BryanOrabutt/cse521_project/automated_functions/data/cattie1.png

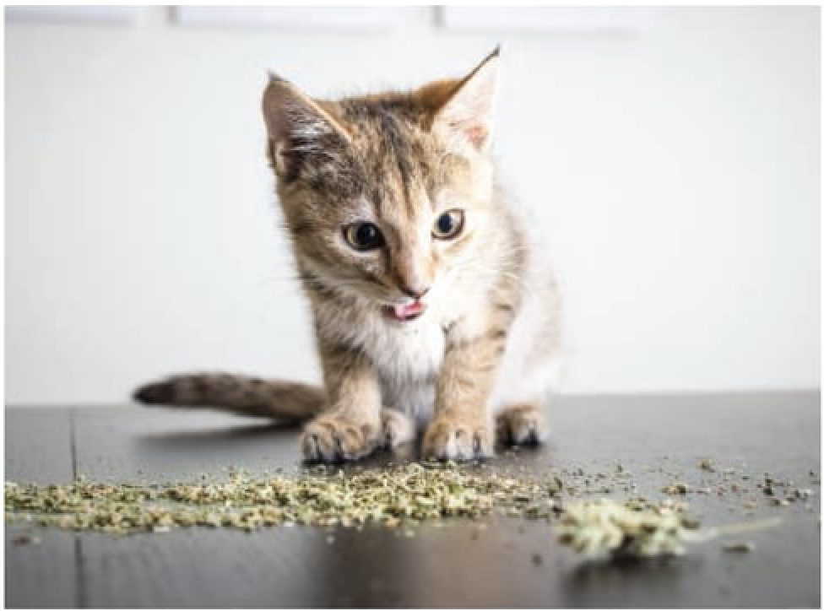
automated_functions/data/cattie1.png
