BryanOrabutt/cse521_project/automated_functions/data/69528761_480x640.jpg

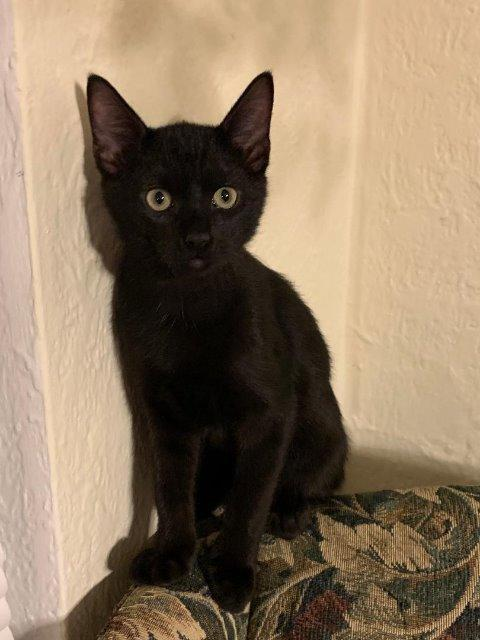
automated_functions/data/69528761_480x640.jpg
