BryanOrabutt/cse521_project/automated_functions/data/69528762_500x375.jpg

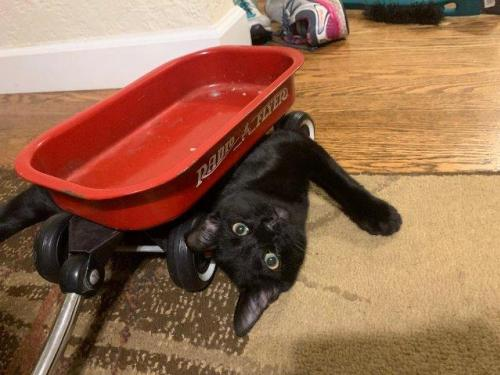
automated_functions/data/69528762_500x375.jpg
