BryanOrabutt/cse521_project/automated_functions/data/cat1.png

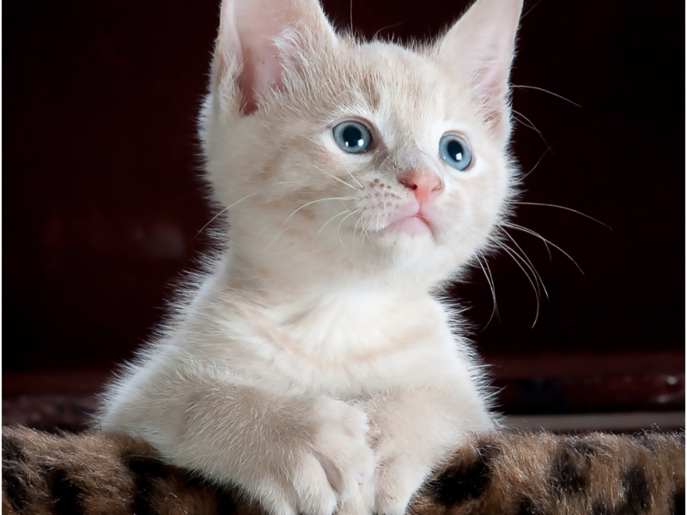
automated_functions/data/cat1.png
