BryanOrabutt/cse521_project/automated_functions/data/cat3.jpg

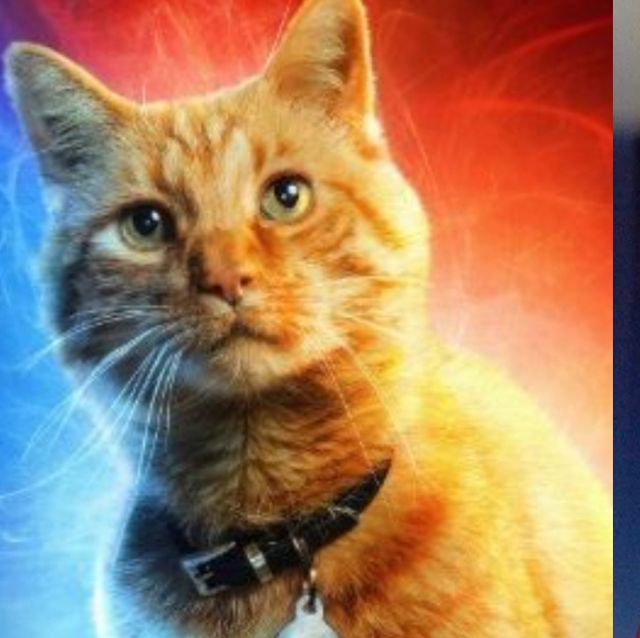
automated_functions/data/cat3.jpg
