BryanOrabutt/cse521_project/automated_functions/data/cat4.jpg

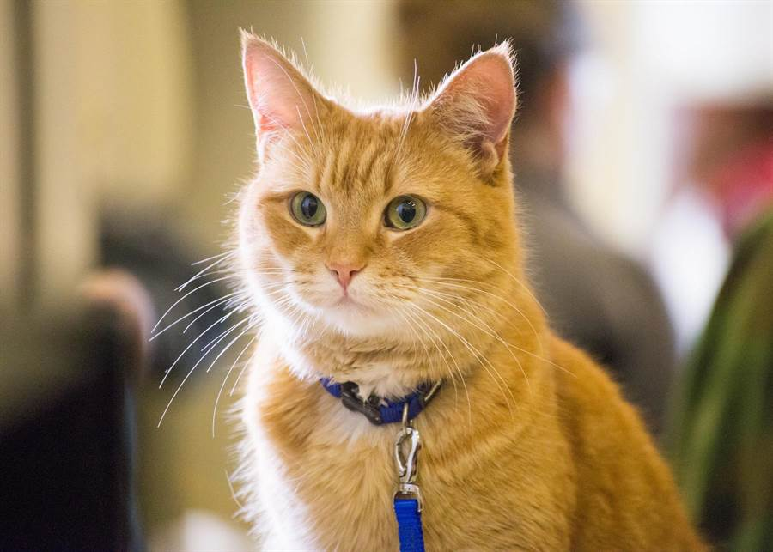
automated_functions/data/cat4.jpg
