BryanOrabutt/cse521_project/automated_functions/data/cat5.jpg

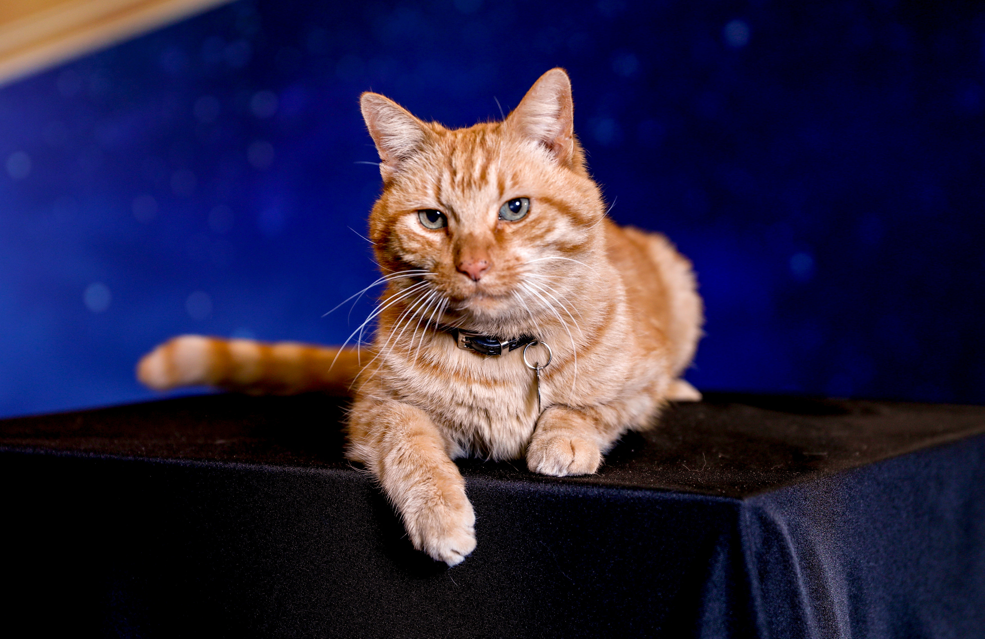
automated_functions/data/cat5.jpg
