BryanOrabutt/cse521_project/automated_functions/data/cattie2.png

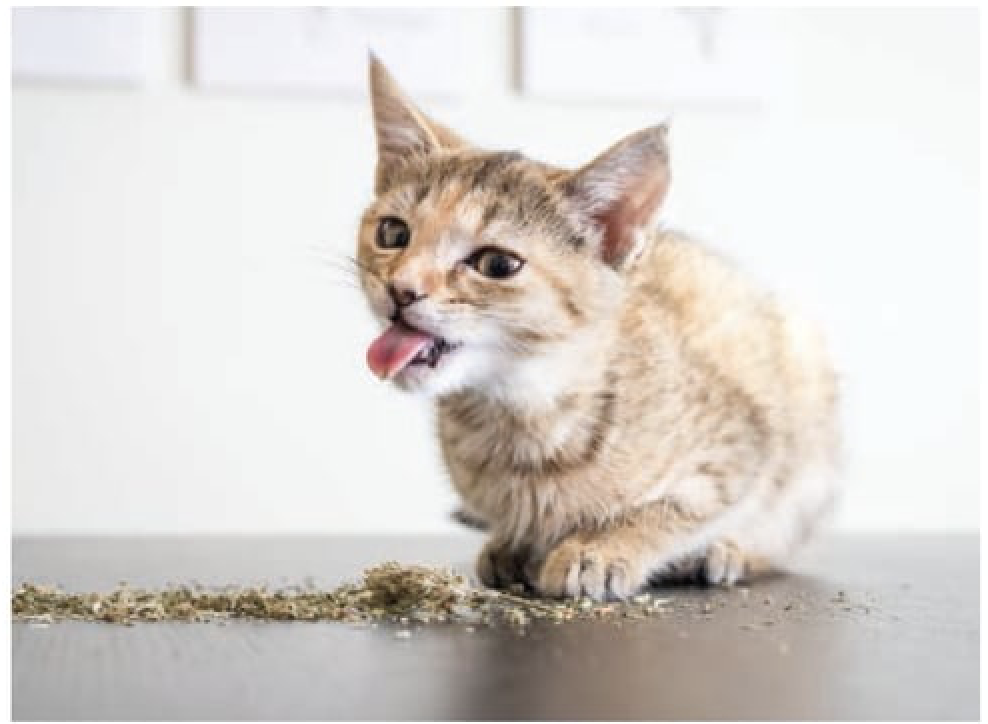
automated_functions/data/cattie2.png
