BryanOrabutt/cse521_project/automated_functions/data/cattie3.png

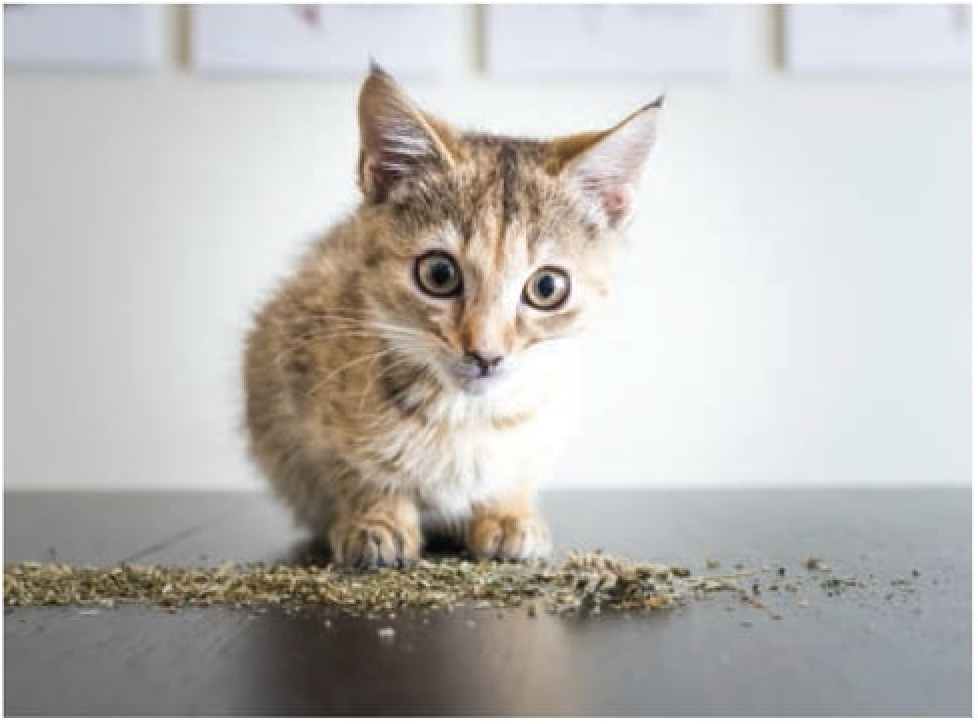
automated_functions/data/cattie3.png
