BryanOrabutt/cse521_project/automated_functions/data/cattie4.png

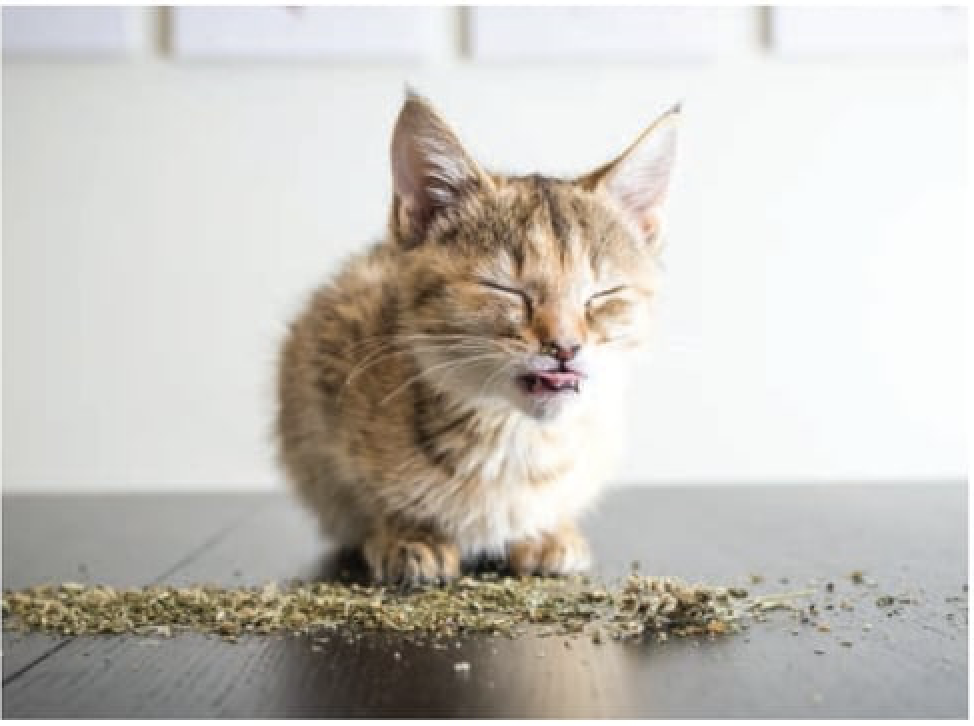
automated_functions/data/cattie4.png
