BryanOrabutt/cse521_project/espressif_code/examples/mcpwm_servo_control/main/mcpwm_servo_control_example.c

/* servo motor control example

   This example code is in the Public Domain (or CC0 licensed, at your option.)

   Unless required by applicable law or agreed to in writing, this
   software is distributed on an "AS IS" BASIS, WITHOUT WARRANTIES OR
   CONDITIONS OF ANY KIND, either express or implied.
*/
#include <stdio.h>

#include "freertos/FreeRTOS.h"
#include "freertos/task.h"
#include "freertos/timers.h"
#include "esp_attr.h"

#include "driver/mcpwm.h"
#include "soc/mcpwm_reg.h"
#include "soc/mcpwm_struct.h"

//You can get these value from the datasheet of servo you use, in general pulse width varies between 1000 to 2000 mocrosecond
#define SERVO_MIN_PULSEWIDTH 1000 //Minimum pulse width in microsecond
#define SERVO_MAX_PULSEWIDTH 2000 //Maximum pulse width in microsecond
#define SERVO_MAX_DEGREE 180 //Maximum angle in degree upto which servo can rotate

char flag = 0;

static void mcpwm_example_gpio_initialize()
{
    printf("initializing mcpwm servo control gpio......\n");
    mcpwm_gpio_init(MCPWM_UNIT_0, MCPWM0A, 18);    //Set GPIO 18 as PWM0A, to which servo is connected
}

/**
 * @brief Use this function to calcute pulse width for per degree rotation
 *
 * @param  degree_of_rotation the angle in degree to which servo has to rotate
 *
 * @return
 *     - calculated pulse width
 */
static uint32_t servo_per_degree_init(uint32_t degree_of_rotation)
{
    uint32_t cal_pulsewidth = 0;
    cal_pulsewidth = (SERVO_MIN_PULSEWIDTH + (((SERVO_MAX_PULSEWIDTH - SERVO_MIN_PULSEWIDTH) * (degree_of_rotation)) / (SERVO_MAX_DEGREE)));
    return cal_pulsewidth;
}

void servo_set(TimerHandle_t xTimer)
{
	uint32_t angle;
	if(flag)
	{
		flag = 0;
		angle = servo_per_degree_init(SERVO_MAX_DEGREE);
		printf("Angle set to: %d\n", SERVO_MAX_DEGREE);
	}
	else
	{
		flag = 1;
		angle = servo_per_degree_init(0);
		printf("Angle set to: %d\n", 0);
	}

	printf("Pulse width set to: %d us\n", angle);

	mcpwm_set_duty_in_us(MCPWM_UNIT_0, MCPWM_TIMER_0, MCPWM_OPR_A, angle);
}

void app_main()
{
    printf("Testing servo motor.......\n");
    //xTaskCreate(mcpwm_example_servo_control, "mcpwm_example_servo_control", 4096, NULL, 5, NULL);'

    //1. mcpwm gpio initialization
    mcpwm_example_gpio_initialize();

    //2. initial mcpwm configuration
    printf("Configuring Initial Parameters of mcpwm......\n");
    mcpwm_config_t pwm_config;
    pwm_config.frequency = 50;    //frequency = 50Hz, i.e. for every servo motor time period should be 20ms
    pwm_config.cmpr_a = 0;    //duty cycle of PWMxA = 0
    pwm_config.cmpr_b = 0;    //duty cycle of PWMxb = 0
    pwm_config.counter_mode = MCPWM_UP_COUNTER;
    pwm_config.duty_mode = MCPWM_DUTY_MODE_0;
    mcpwm_init(MCPWM_UNIT_0, MCPWM_TIMER_0, &pwm_config);    //Configure PWM0A & PWM0B with above settings
	
	TimerHandle_t t0 = xTimerCreate("servo_max_timer", pdMS_TO_TICKS(2000), pdTRUE, (void*) 0, servo_set);
	printf("Timer created...\n");
	xTimerStart(t0, 0);
	printf("Timer started!\n");

}
